AllenNeuralDynamics/exa-spim-hardware/ASI/stage_LS-100-FTP.SLDPRT

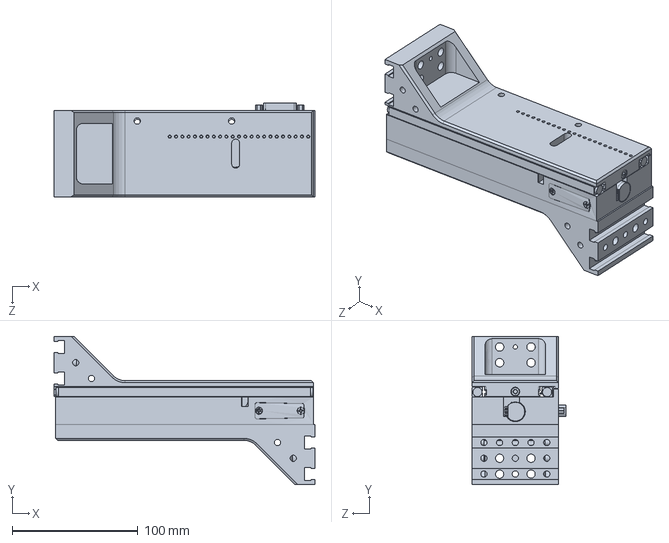
[picture p15: CAD file, 2023-05-30]
ASI/stage_LS-100-FTP.SLDPRT
207.5 x 117.9 x 74.4 mm
