AllenNeuralDynamics/exa-spim-hardware/custom/galvo_clamp_2.SLDPRT

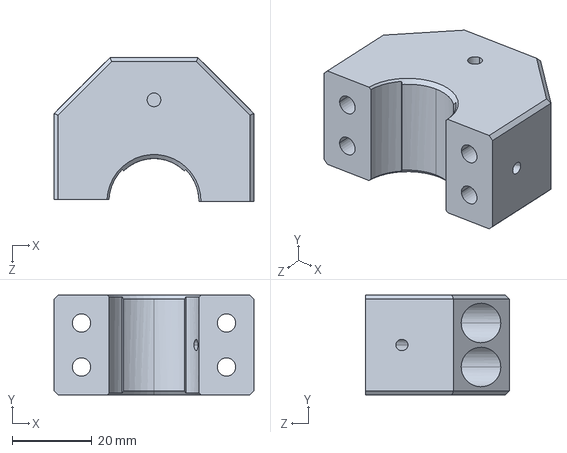
[picture p16: CAD file, 2023-05-30]
custom/galvo_clamp_2.SLDPRT
50.0 x 25.0 x 36.0 mm
