AllenNeuralDynamics/exa-spim-hardware/navitar/navitar_cap.sldprt

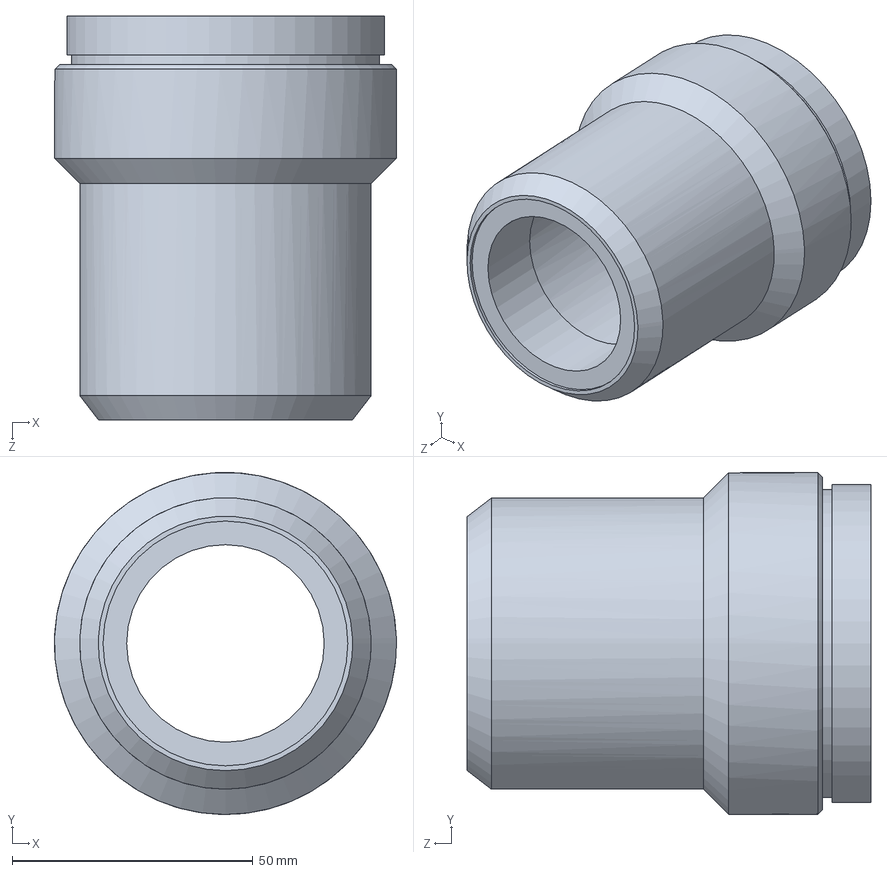
[picture p17: CAD file, 2023-05-30]
navitar/navitar_cap.sldprt
71.0 x 71.0 x 83.8 mm
