AllenNeuralDynamics/exa-spim-hardware/custom/sample_base_0284-200-04.SLDPRT

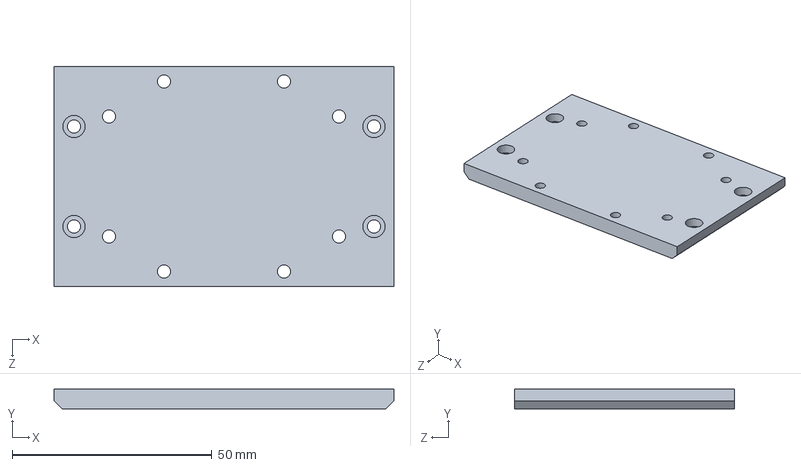
[picture p18: CAD file, 2023-05-30]
custom/sample_base_0284-200-04.SLDPRT
85.0 x 5.00 x 55.0 mm
