AllenNeuralDynamics/exa-spim-hardware/navitar/navitar_adapter.sldprt

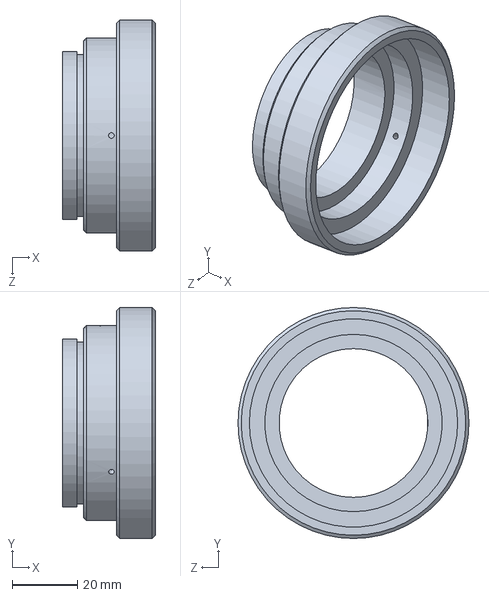
[picture p19: CAD file, 2023-05-30]
navitar/navitar_adapter.sldprt
28.5 x 71.0 x 71.0 mm
