AllenNeuralDynamics/exa-spim-hardware/custom/sample_lid_0284-200-03.SLDPRT

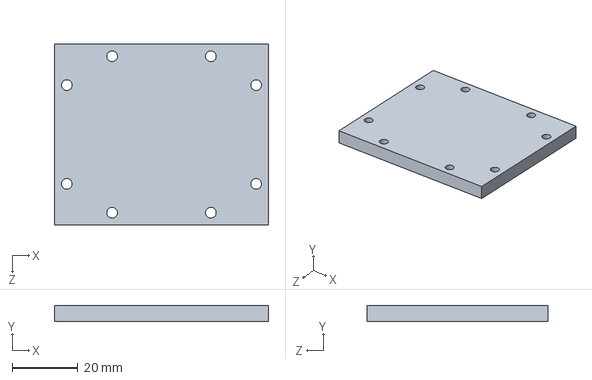
[picture p20: CAD file, 2023-05-30]
custom/sample_lid_0284-200-03.SLDPRT
65.0 x 5.00 x 55.0 mm
