AllenNeuralDynamics/exa-spim-hardware/custom/galvo_holder.SLDPRT

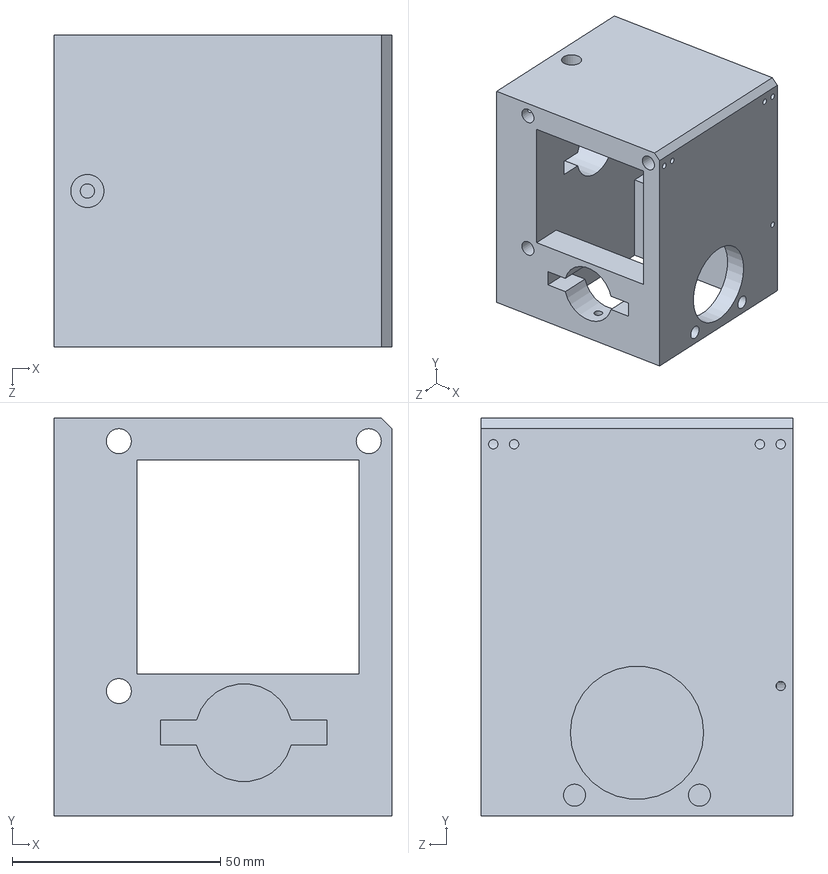
[picture p21: CAD file, 2023-05-30]
custom/galvo_holder.SLDPRT
81.1 x 95.6 x 75.0 mm
