AllenNeuralDynamics/exa-spim-hardware/custom/window.SLDPRT

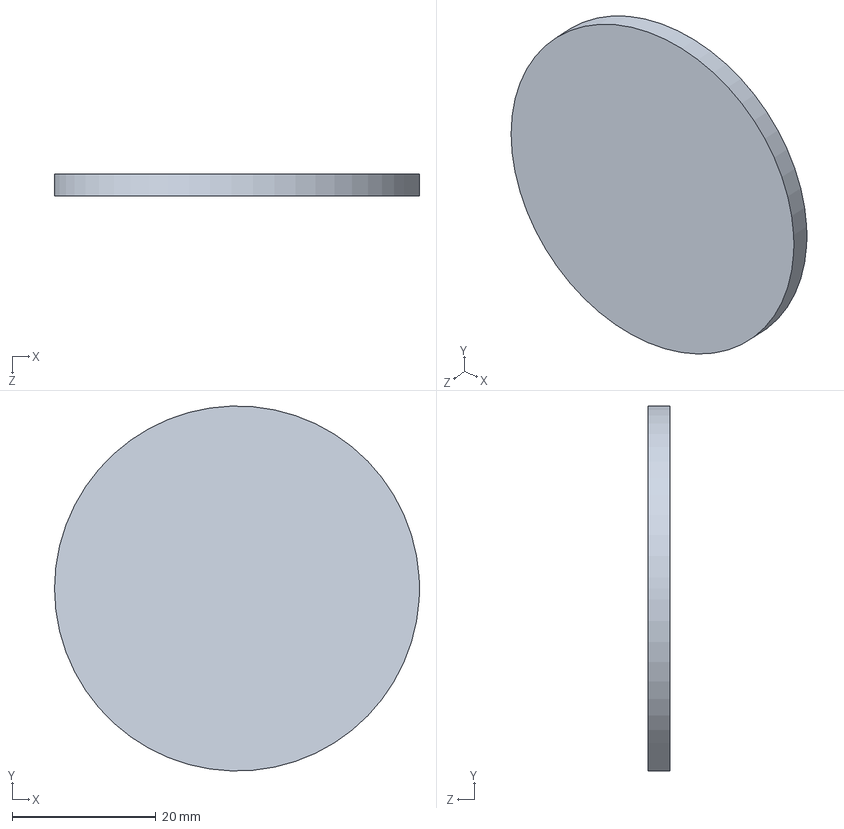
[picture p22: CAD file, 2023-05-30]
custom/window.SLDPRT
50.8 x 50.8 x 3.00 mm
