AllenNeuralDynamics/exa-spim-hardware/navitar/navitar_window.SLDPRT

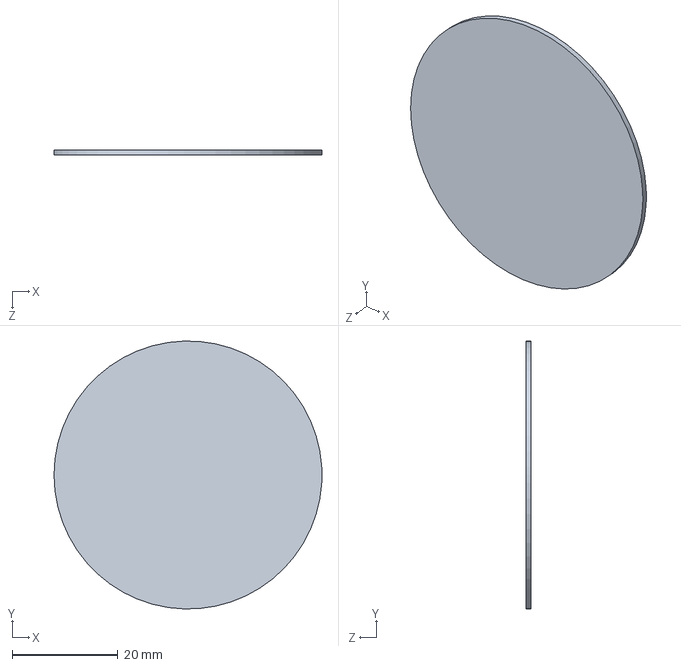
[picture p23: CAD file, 2023-05-30]
navitar/navitar_window.SLDPRT
50.8 x 50.8 x 1.00 mm
