AllenNeuralDynamics/exa-spim-hardware/custom/laser_box.SLDPRT

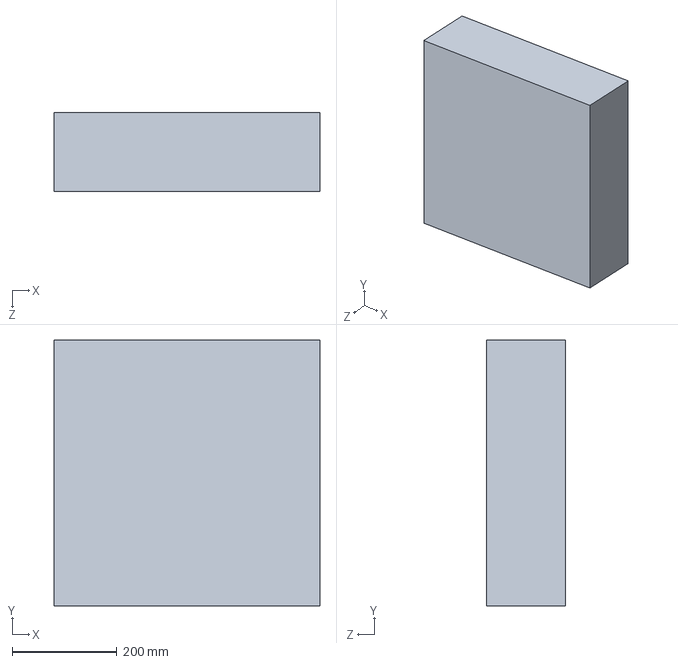
[picture p24: CAD file, 2023-05-30]
custom/laser_box.SLDPRT
508.0 x 508.0 x 150.0 mm
