AllenNeuralDynamics/exa-spim-hardware/custom/galvo_holder V2.SLDPRT

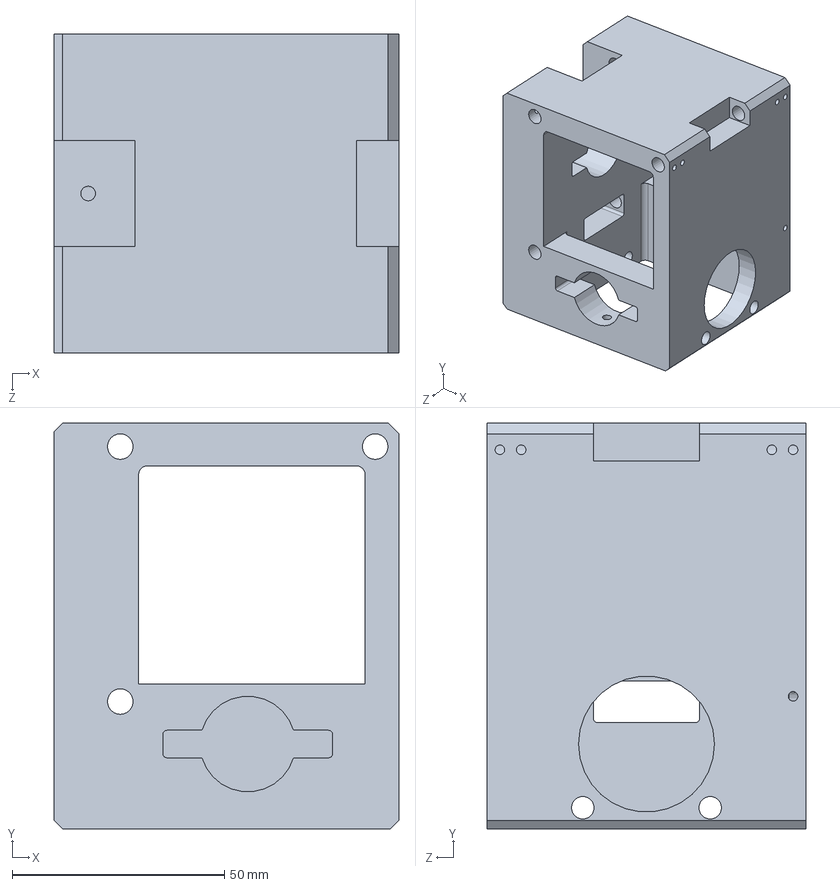
[picture p25: CAD file, 2023-05-30]
custom/galvo_holder V2.SLDPRT
81.1 x 95.6 x 75.0 mm
