AllenNeuralDynamics/exa-spim-hardware/custom/u_mount_0284-100-01.SLDPRT

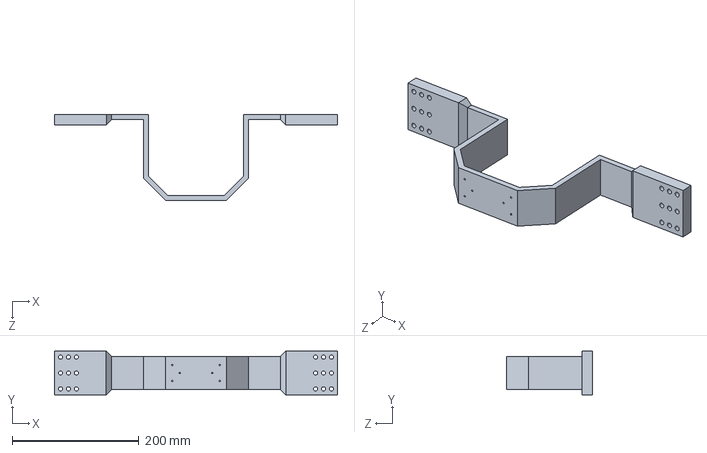
[picture p26: CAD file, 2023-05-30]
custom/u_mount_0284-100-01.SLDPRT
446.0 x 68.6 x 136.0 mm
