AllenNeuralDynamics/exa-spim-hardware/custom/sample_wall_0284-200-02.SLDPRT

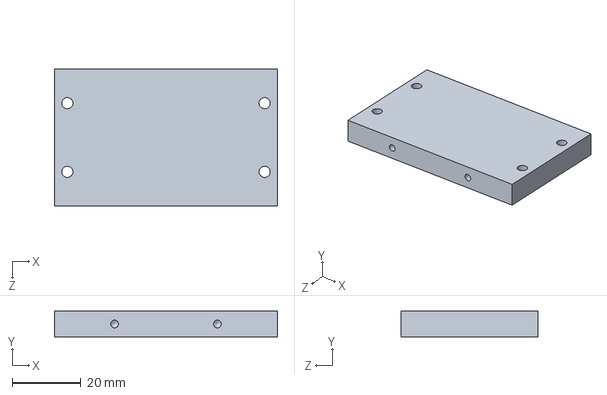
[picture p27: CAD file, 2023-05-30]
custom/sample_wall_0284-200-02.SLDPRT
65.0 x 7.50 x 40.0 mm
