AllenNeuralDynamics/exa-spim-hardware/custom/galvo_clamp_1.SLDPRT

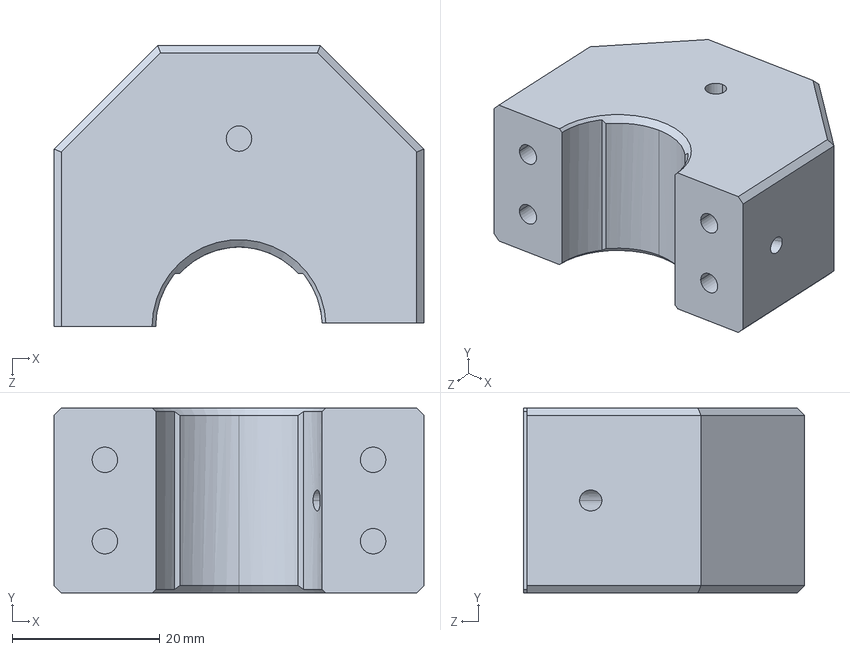
[picture p28: CAD file, 2023-05-30]
custom/galvo_clamp_1.SLDPRT
50.0 x 25.0 x 38.0 mm
