AllenNeuralDynamics/exa-spim-hardware/custom/Shibuya_HLB_5X.SLDPRT

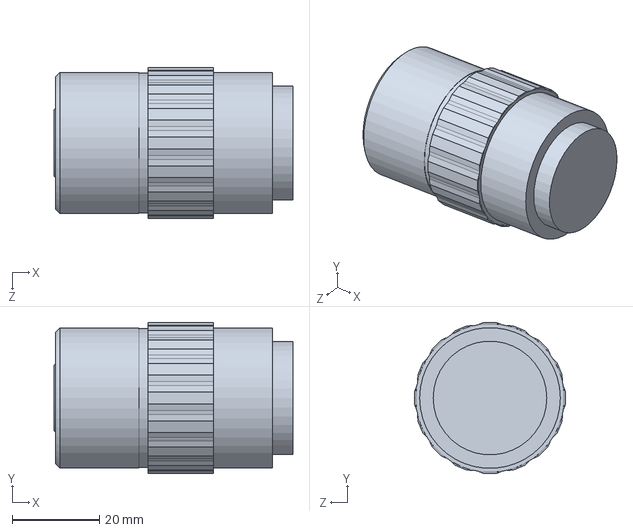
[picture p29: CAD file, 2023-05-30]
custom/Shibuya_HLB_5X.SLDPRT
54.7 x 34.6 x 34.6 mm
